chadaustin/wired-sculpt-pcb/outputs/2020-12-20 Rev2 PCBWay/fixed anode indication.png

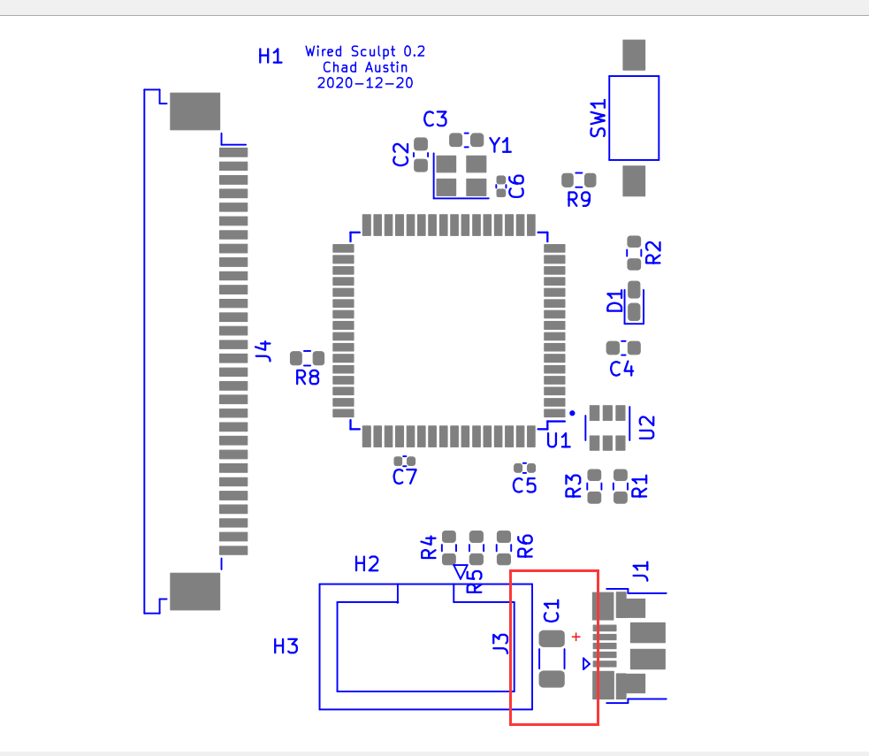
outputs/2020-12-20 Rev2 PCBWay/fixed anode indication.png
